mecargill/radar_proj/figures/corner_refl_7-5_walk_away.png

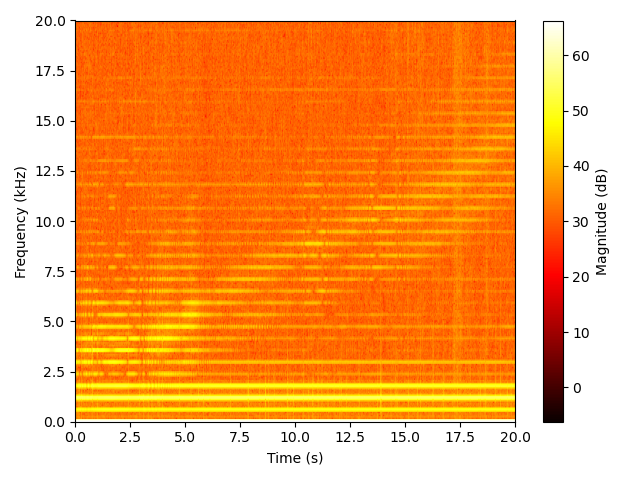
figures/corner_refl_7-5_walk_away.png
