mecargill/radar_proj/sp/baseline_doppler.gif

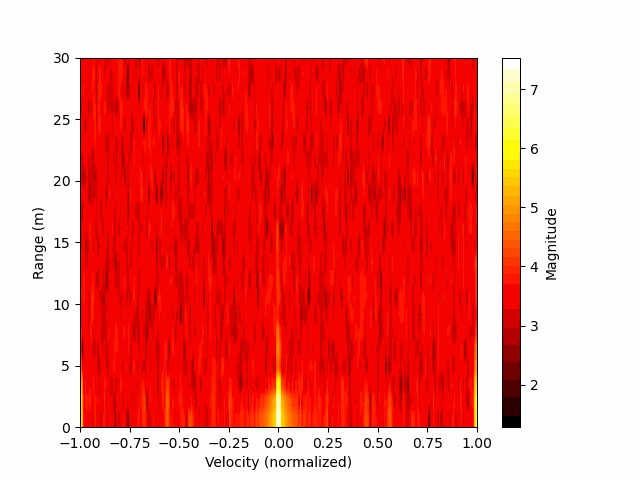
sp/baseline_doppler.gif
