mecargill/radar_proj/figures/first_car_test.png

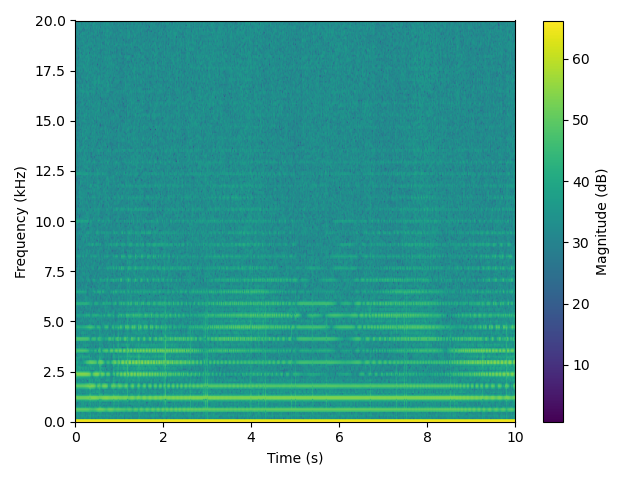
figures/first_car_test.png
