mecargill/radar_proj/sim.asc

C1: cap; 470n
C2: cap; 5n
C3: cap; 5n
L1: ind; 19.3µ
R1: res; 50
R2: res; 10000000
R3: res; 10000
R4: res; 1268
R5: res; 11412
V1: voltage; SINE(0 1.8 10000000 0 0 0 10000); AC 1
V2: voltage; 3.3
Named nets: 0, src, out, bias1
.tran 0 0.005 0
